rgulland/Portable-PCB-Reflow-Plate/CAD/COTS/PTC Resistive Heater.SLDPRT

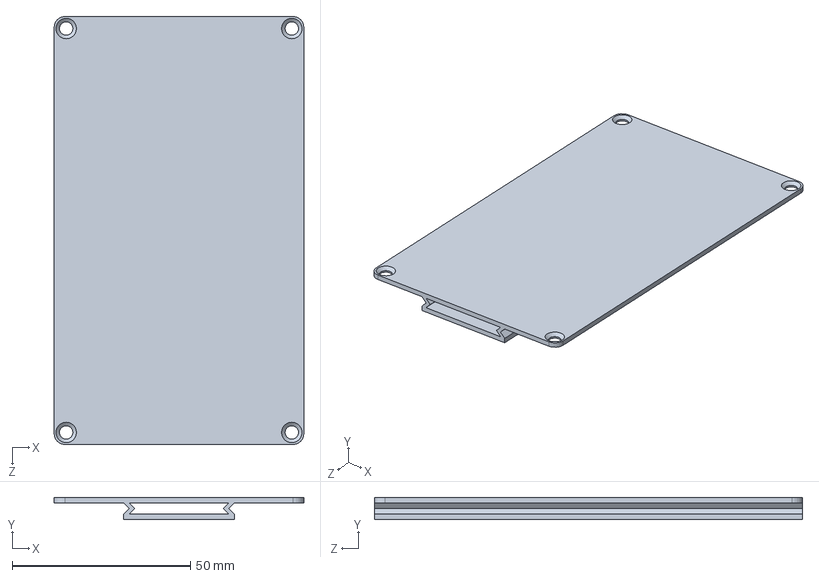
[picture p15: CAD file, 2022-03-18]
CAD/COTS/PTC Resistive Heater.SLDPRT
70.0 x 6.20 x 120.0 mm
