rgulland/Portable-PCB-Reflow-Plate/CAD/COTS/PCB Backplane.SLDPRT

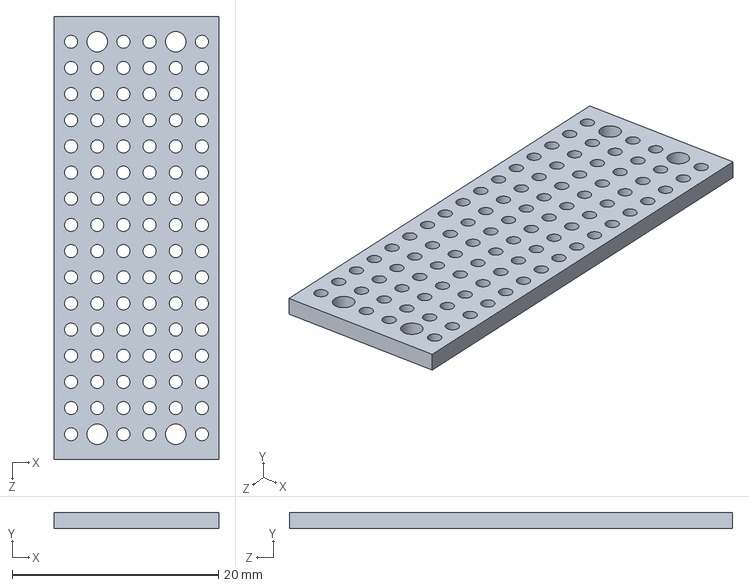
[picture p16: CAD file, 2022-03-18]
CAD/COTS/PCB Backplane.SLDPRT
16.0 x 1.60 x 43.0 mm
